metan-ucw/parkside-repair/kicad/trans.kicad_sch

## KiCad design kicad/trans.kicad_sch (2024-05-16)

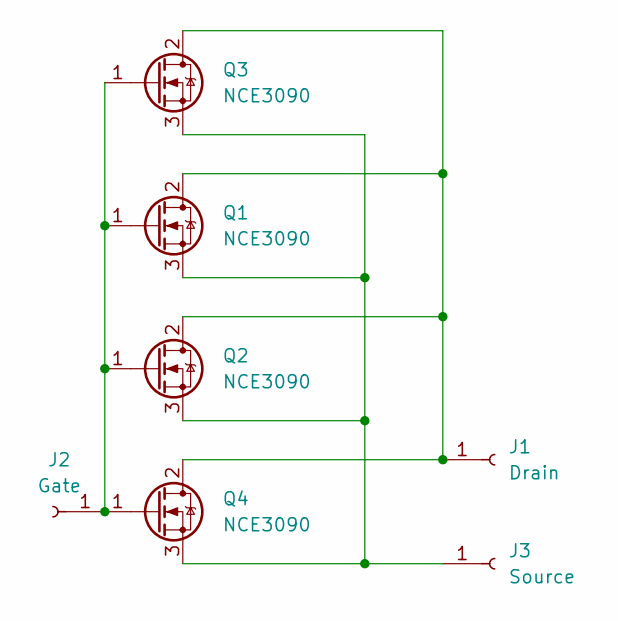
[picture p4: schematic trans.kicad_sch]

Parts:
J1: Drain; SolderWire-1.5sqmm_1x01_D1.7mm_OD3.9mm
J2: Gate; SolderWire-0.75sqmm_1x01_D1.25mm_OD2.3mm
J3: Source; SolderWire-1.5sqmm_1x01_D1.7mm_OD3.9mm
Q1, Q2, Q3, Q4: NCE3090; TO-252-2

Connections:
unnamed: J1.1, Q1.2 (D), Q2.2 (D), Q3.2 (D), Q4.2 (D)
unnamed: J2.1, Q1.1 (G), Q2.1 (G), Q3.1 (G), Q4.1 (G)
unnamed: J3.1, Q1.3 (S), Q2.3 (S), Q3.3 (S), Q4.3 (S)
